cgn00/Packaging-Machine-Board-/librarys/adafruit-teensy-3-2-header-1.snapshot.2/2756-02.jpg

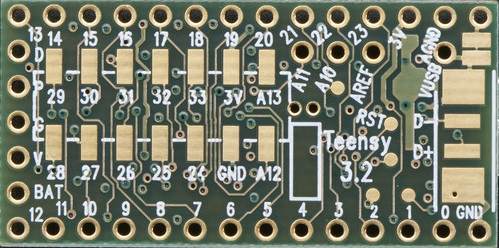
librarys/adafruit-teensy-3-2-header-1.snapshot.2/2756-02.jpg
